za3k/zorchpad/src/case_openscad/top_plate_rounded.stl

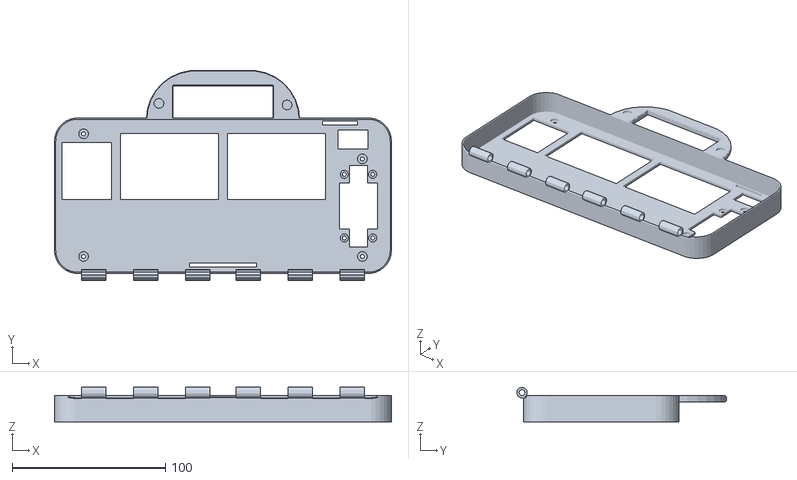
[picture p20: CAD file, 2024-06-25]
src/case_openscad/top_plate_rounded.stl
219.7 x 136.7 x 22.5
