za3k/zorchpad/src/kicad/keyboard/12x5.kicad_sch

## KiCad design src/kicad/keyboard/12x5.kicad_sch (2025-04-08)


Parts:
D65, D66, D67, D68, D69, D70, D71, D72, D73, D74, D75, D76, D77, D78, D79, D80, D81, D82, D83, D84, D85, D86, D87, D88, D89, D90, D91, D92, D93, D94, D95, D96, D97, D98, D99, D100, D101, D102, D103, D105, D106, D107, D108, D110, D111, D113, D114, D115, D116, D117, D118, D119, D121, D122, D123, D124, D125, D126, D127: D
KEY_11, KEY_12, KEY_13, KEY_14, KEY_15, KEY_16, KEY_17, KEY_18, KEY_19, KEY_20: SW_Push
KEY_A2: SW_Push
KEY_ALT2: SW_Push
KEY_B2: SW_Push
KEY_BACK2: SW_Push
KEY_C2: SW_Push
KEY_COMMA2: SW_Push
KEY_CTRL2: SW_Push
KEY_D2: SW_Push
KEY_DOWN2: SW_Push
KEY_E2: SW_Push
KEY_EQUALS2: SW_Push
KEY_ESC2: SW_Push
KEY_F2: SW_Push
KEY_FN2: SW_Push
KEY_G2: SW_Push
KEY_H2: SW_Push
KEY_I2: SW_Push
KEY_J2: SW_Push
KEY_K2: SW_Push
KEY_L2: SW_Push
KEY_LEFT2: SW_Push
KEY_M2: SW_Push
KEY_MINUS2: SW_Push
KEY_N2: SW_Push
KEY_O2: SW_Push
KEY_OS2: SW_Push
KEY_P2: SW_Push
KEY_PERIOD2: SW_Push
KEY_Q2: SW_Push
KEY_QUOTE2: SW_Push
KEY_R2: SW_Push
KEY_RET3, KEY_RET4: SW_Push
KEY_RIGHT2: SW_Push
KEY_S2: SW_Push
KEY_SC2: SW_Push
KEY_SHIFT2: SW_Push
KEY_SLASH2: SW_Push
KEY_SPACE3, KEY_SPACE4: SW_Push
KEY_T2: SW_Push
KEY_TAB2: SW_Push
KEY_U2: SW_Push
KEY_UP2: SW_Push
KEY_V2: SW_Push
KEY_W2: SW_Push
KEY_X2: SW_Push
KEY_Y2: SW_Push
KEY_Z2: SW_Push
Pull-Up9, Pull-Up10, Pull-Up11, Pull-Up12, Pull-Up13, Pull-Up14, Pull-Up15, Pull-Up16: 1K

Connections:
1: D65.1 (K), D66.1 (K), D67.1 (K), D68.1 (K), D69.1 (K), D70.1 (K), D71.1 (K), D72.1 (K), D73.1 (K), D74.1 (K), D75.1 (K), D76.1 (K), D77.1 (K), D78.1 (K), D79.1 (K), D80.1 (K), D81.1 (K), D82.1 (K), D83.1 (K), D84.1 (K), D85.1 (K), D86.1 (K), D87.1 (K), D88.1 (K), D89.1 (K), D90.1 (K), D91.1 (K), D92.1 (K), D93.1 (K), D94.1 (K), D95.1 (K), D96.1 (K), D97.1 (K), D98.1 (K), D99.1 (K), D100.1 (K), D101.1 (K), D102.1 (K), D103.1 (K), D105.1 (K), D106.1 (K), D107.1 (K), D108.1 (K), D110.1 (K), D111.1 (K), D113.1 (K), D114.1 (K), D115.1 (K), D116.1 (K), D117.1 (K), D118.1 (K), D119.1 (K), D121.1 (K), D122.1 (K), D123.1 (K), D124.1 (K), D125.1 (K), D126.1 (K), D127.1 (K), KEY_K2.1, KEY_L2.1, KEY_QUOTE2.1, KEY_SC2.1, Pull-Up16.2
+3.3V: Pull-Up9.1, Pull-Up10.1, Pull-Up11.1, Pull-Up12.1, Pull-Up13.1, Pull-Up14.1, Pull-Up15.1, Pull-Up16.1
Input 1: KEY_11.1, KEY_13.1, KEY_15.1, KEY_16.1, KEY_17.1, KEY_18.1, KEY_19.1, KEY_20.1, Pull-Up9.2
Input 2: KEY_E2.1, KEY_Q2.1, KEY_R2.1, KEY_T2.1, KEY_TAB2.1, KEY_U2.1, KEY_W2.1, KEY_Y2.1, Pull-Up10.2
Input 3: KEY_A2.1, KEY_D2.1, KEY_ESC2.1, KEY_F2.1, KEY_G2.1, KEY_H2.1, KEY_J2.1, KEY_S2.1, Pull-Up11.2
Input 4: KEY_B2.1, KEY_C2.1, KEY_M2.1, KEY_N2.1, KEY_SHIFT2.1, KEY_V2.1, KEY_X2.1, KEY_Z2.1, Pull-Up12.2
Input 5: KEY_ALT2.1, KEY_CTRL2.1, KEY_OS2.1, KEY_RET3.1, KEY_RET4.1, KEY_SPACE3.1, KEY_SPACE4.1, Pull-Up13.2
Input 6: KEY_12.1, KEY_14.1, KEY_COMMA2.1, KEY_EQUALS2.1, KEY_MINUS2.1, KEY_PERIOD2.1, KEY_SLASH2.1, KEY_UP2.1, Pull-Up14.2
Input 7: KEY_BACK2.1, KEY_DOWN2.1, KEY_FN2.1, KEY_I2.1, KEY_LEFT2.1, KEY_O2.1, KEY_P2.1, KEY_RIGHT2.1, Pull-Up15.2
unnamed: D65.2 (A), KEY_11.2
unnamed: D66.2 (A), KEY_TAB2.2
unnamed: D67.2 (A), KEY_ESC2.2
unnamed: D68.2 (A), KEY_SHIFT2.2
unnamed: D69.2 (A), KEY_CTRL2.2
unnamed: D70.2 (A), KEY_12.2
unnamed: D71.2 (A), KEY_I2.2
unnamed: D72.2 (A), KEY_K2.2
unnamed: D73.2 (A), KEY_13.2
unnamed: D74.2 (A), KEY_Q2.2
unnamed: D75.2 (A), KEY_A2.2
unnamed: D76.2 (A), KEY_Z2.2
unnamed: D77.2 (A), KEY_OS2.2
unnamed: D78.2 (A), KEY_14.2
unnamed: D79.2 (A), KEY_O2.2
unnamed: D80.2 (A), KEY_L2.2
unnamed: D81.2 (A), KEY_15.2
unnamed: D82.2 (A), KEY_W2.2
unnamed: D83.2 (A), KEY_S2.2
unnamed: D84.2 (A), KEY_X2.2
unnamed: D85.2 (A), KEY_ALT2.2
unnamed: D86.2 (A), KEY_MINUS2.2
unnamed: D87.2 (A), KEY_P2.2
unnamed: D88.2 (A), KEY_SC2.2
unnamed: D89.2 (A), KEY_16.2
unnamed: D90.2 (A), KEY_E2.2
unnamed: D91.2 (A), KEY_D2.2
unnamed: D92.2 (A), KEY_C2.2
unnamed: D93.2 (A), KEY_SPACE3.2
unnamed: D94.2 (A), KEY_EQUALS2.2
unnamed: D95.2 (A), KEY_BACK2.2
unnamed: D96.2 (A), KEY_QUOTE2.2
unnamed: D97.2 (A), KEY_17.2
unnamed: D98.2 (A), KEY_R2.2
unnamed: D99.2 (A), KEY_F2.2
unnamed: D100.2 (A), KEY_V2.2
unnamed: D101.2 (A), KEY_SPACE4.2
unnamed: D102.2 (A), KEY_COMMA2.2
unnamed: D103.2 (A), KEY_FN2.2
unnamed: D105.2 (A), KEY_18.2
unnamed: D106.2 (A), KEY_T2.2
unnamed: D107.2 (A), KEY_G2.2
unnamed: D108.2 (A), KEY_B2.2
unnamed: D110.2 (A), KEY_PERIOD2.2
unnamed: D111.2 (A), KEY_LEFT2.2
unnamed: D113.2 (A), KEY_19.2
unnamed: D114.2 (A), KEY_Y2.2
unnamed: D115.2 (A), KEY_H2.2
unnamed: D116.2 (A), KEY_N2.2
unnamed: D117.2 (A), KEY_RET3.2
unnamed: D118.2 (A), KEY_UP2.2
unnamed: D119.2 (A), KEY_DOWN2.2
unnamed: D121.2 (A), KEY_20.2
unnamed: D122.2 (A), KEY_U2.2
unnamed: D123.2 (A), KEY_J2.2
unnamed: D124.2 (A), KEY_M2.2
unnamed: D125.2 (A), KEY_RET4.2
unnamed: D126.2 (A), KEY_SLASH2.2
unnamed: D127.2 (A), KEY_RIGHT2.2

Notes on the sheet:
Inputs, Pull-up high
Outputs (Low)
